Staacks/gbinterceptor/firmware/screens/default.png

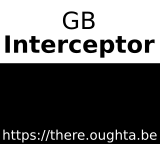
firmware/screens/default.png
