Staacks/gbinterceptor/firmware/jpeg/jpeg.h

#ifndef GBINTERCEPTOR_JPEG
#define GBINTERCEPTOR_JPEG

#include "pico/stdlib.h"
#include "ppu.h"

#define JPEG_DATA_SIZE (SCREEN_SIZE * 5 / 8) //5bit per pixel, see https://github.com/Staacks/gbinterceptor/issues/17
#define JPEG_HEADER_SIZE 188
#define JPEG_HEADER_SIZE_NO_CHROMA 160
#define JPEG_END_SIZE 2895
#define JPEG_END_SIZE_NO_CHROMA 2
#define FRAME_SIZE (JPEG_DATA_SIZE + JPEG_HEADER_SIZE + JPEG_END_SIZE)
#define FRAME_SIZE_NO_CHROMA (JPEG_DATA_SIZE + JPEG_HEADER_SIZE_NO_CHROMA + JPEG_END_SIZE_NO_CHROMA)

#define JPEG_CHROMA_OFFSET (JPEG_HEADER_SIZE + JPEG_DATA_SIZE + 12)

void prepareJpegEncoding();
void startBackbufferToJPEG(bool allowFrameBlend);
void continueBackbufferToJPEG();

#endif
